arthchav/vitis/Fichiers/Weekly Report/~ Arthur Report/Séance n°06 - 06.12.22.pdf

Arthur | Rapport de séance n°6 | Projet Vitis
| | 6/12/22

Objectifs de la séance :

- Installation Arduino Mega
- Pouvoir brancher notre Robot à une prise 240v
- Installer le robot sur son nouveau châssis
- Coder les 2 capteurs IR pour faire tourner le robot

Réalisations :

- Le transfert de l’Arduino Uno à la Mega était nécessaire étant donné le nombre de pins nécessaire aux capteurs. Ce fût assez facile puisqu’il y a juste à recopier les branchements sur la nouvelle carte.

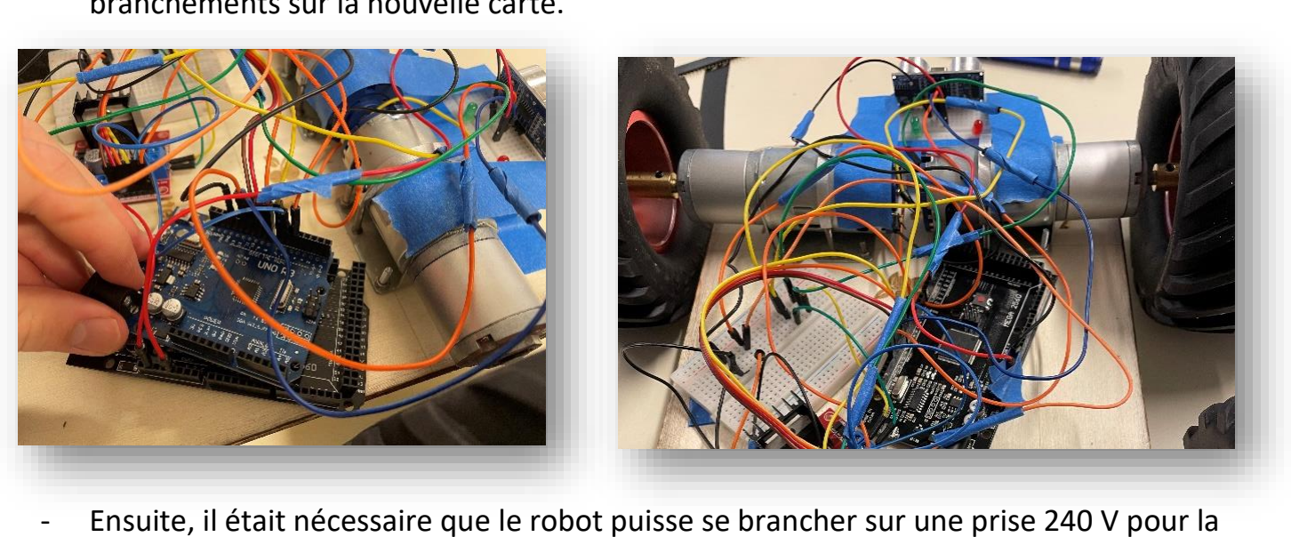
[picture p20: figure]

- Ensuite, il était nécessaire que le robot puisse se brancher sur une prise 240 V pour la suite de nos expériences. Jusqu’à présent nous utilisions les alimentations variables disponibles sur les paillasses.

Le professeur a pris de l’avance en faisant les branchements sur une alimentation afin de transformer le 240V alternatif en 12V continu.
Il fallait maintenant pouvoir alimenter la carte Arduino par le port prévu à cet effet ainsi que le Pont en H pour fournir l’énergie nécessaire aux moteurs.
Pour cela j’ai utilisé un domino d’électricien qui me permet d’obtenir 2 sorties. Enfin pour débrancher/brancher le tout facilement j’ai connecté une prise male femelle sur le domino et la sortie 12V. Montage ci-dessous.

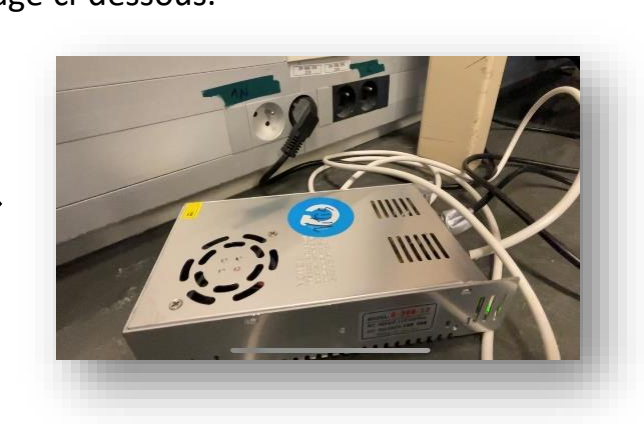
[picture p21: figure]
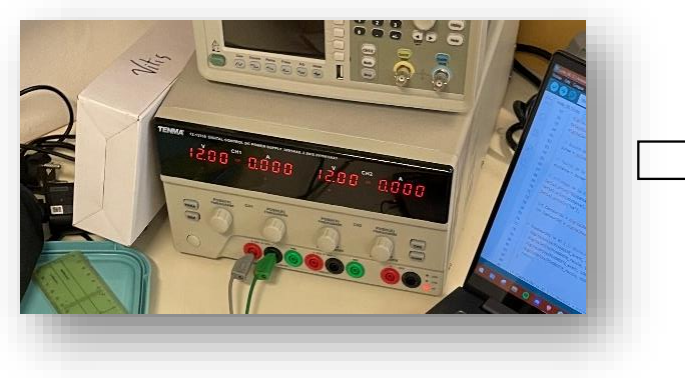
[picture p22: figure]

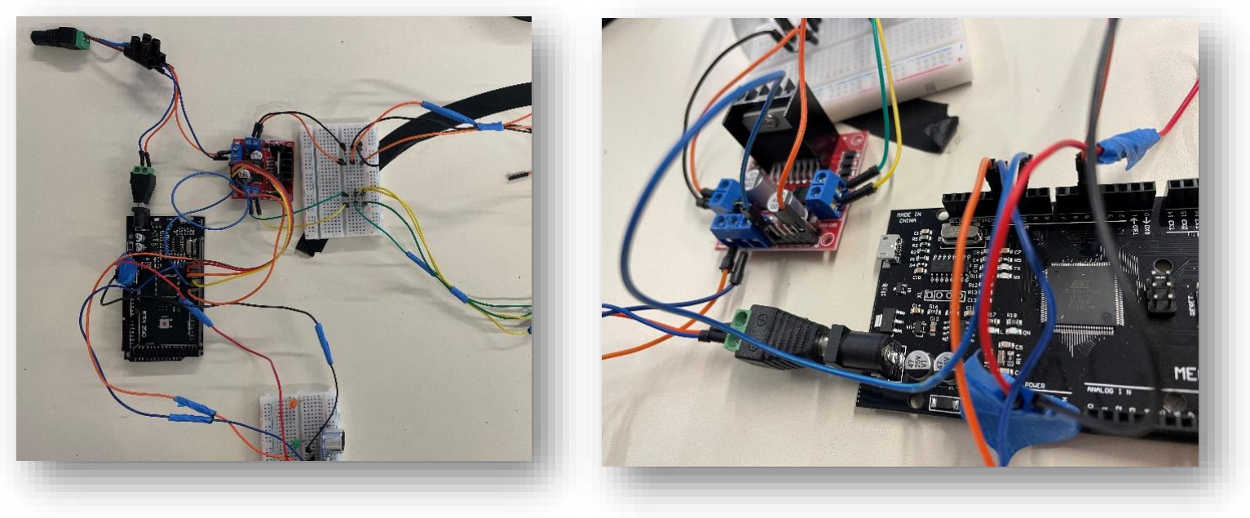
[picture p23: figure]

- Tanguy s’est chargé de fixer le robot sur le nouveau châssis et je me suis chargé de refaire les branchements un peu plus proprement.

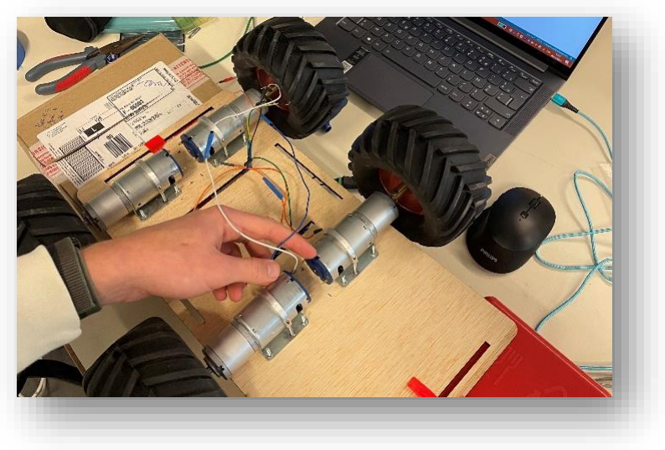
[picture p24: figure]

- Une fois cela il faut maintenant que notre robot puisse se diriger dans l’espace. Pour cela nous avons fait le choix de fixer 2 capteurs IR sur l’avant droite et gauche du robot.
Pour la partie code c’est assez simple (voir fin du doc).
- Un fois ce petit bout de code ajouté à l’ancien il était temps de faire fonctionner notre robot sur une prise 240V. Cependant plongé dans la réalisation du robot je n’ai pas réfléchi au fait que les câbles Arduino sont conçus pour transférer du 5V à basse intensité. Voici le résultat :

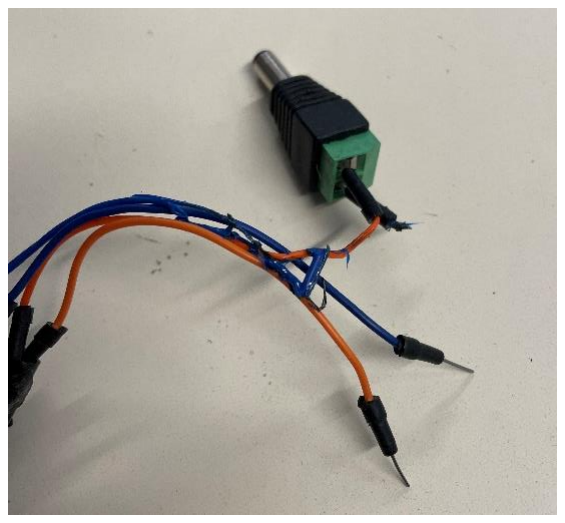
[picture p25: figure]

Des câbles complétement fondus. Reste plus qu’à changer ces câbles pour tester notre code !

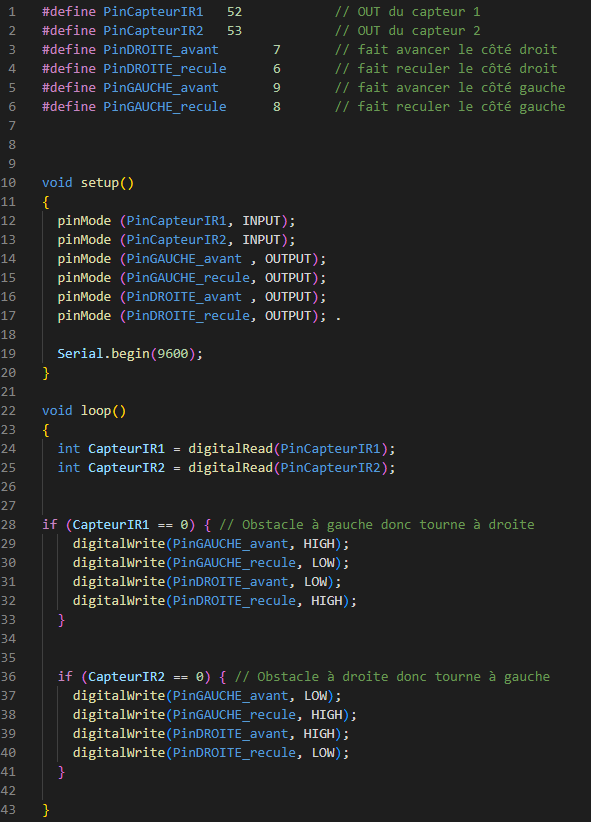
[picture p26: page 3]
