arthchav/vitis/Fichiers/Weekly Report/~ Tanguy Report/Rapport de séance n°9.pdf

Rapport de Séance 15/12/22

Objectifs de séance:
-Modélisation du porte-outils
I-Modélisation du porte-outils

Pendant cette séance j’ai continué la modélisation du porte-outils sur fusion, la difficulté est de réussir à avoir un ensemble cohérent et soudé afin d’avoir le résultat souhaité. J’ai rencontré beaucoup de difficulté afin que les pièces soient bien imbriqué et que les liaisons ce fasse bien.

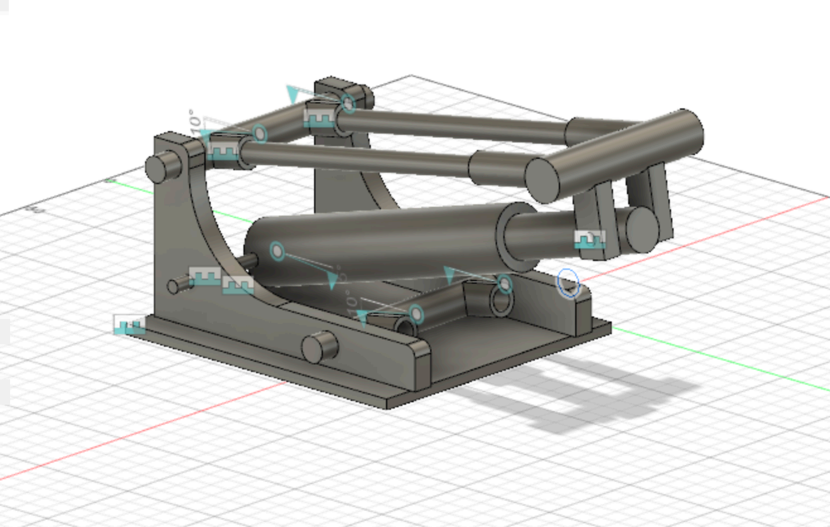
[picture p83: figure]

L’objectif pour la rentré est d’obtenir une modélisation satisfaisante afin de lancer l’impression des pièces.
