arthchav/vitis/Fichiers/Weekly Report/~ Arthur Report/Séance n°03 - 28.10.22.pdf

Arthur | Rapport de séance n°3 | Projet Vitis
| | 28/10/22

Objectifs de la séance :

- Découper le châssis
- Découverte GPS et tenter d’avoir une position

Réalisations :

- J’ai consacré la première partie de la séance à la découpe du châssis, le fichier svg étant prêt depuis la semaine dernière il ne restait plus qu’à lancer l’impression. Afin de pourvoir fixer le moteur et la batterie, le châssis (en bois) se devait d’être le plus rigide possible.
Le contreplaqué 5 mm était donc une bonne solution.

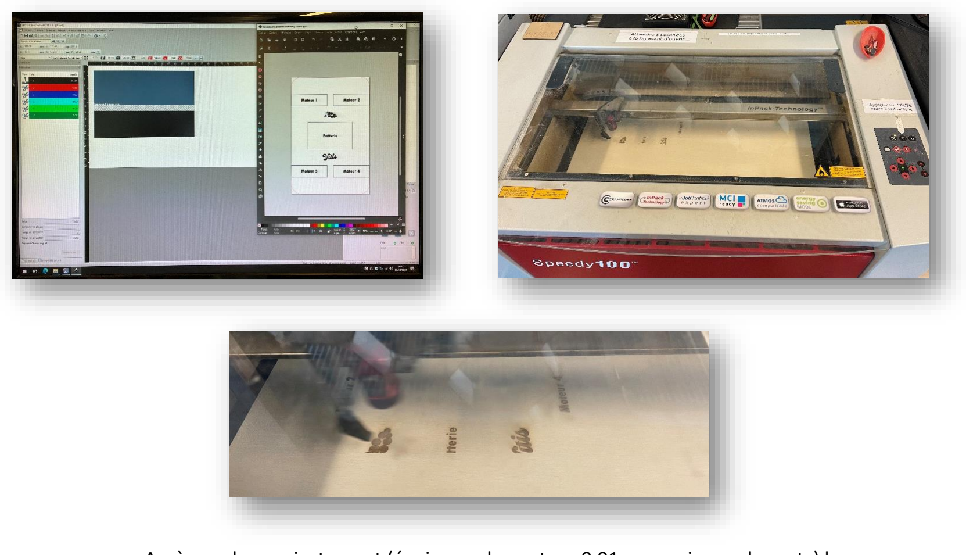
[picture p94: figure]

Après quelques ajustement (épaisseur du contour 0.01, mauvaise couleur etc) la gravure s’est bien déroulée.
Le problème est que le FabLab ont de nouveaux fournisseurs de bois, le contreplaqué 5 mm fournit ne se découpait pas avec les paramètres 5 mm de la machine. Après plusieurs essais de découpe sur une chute de ce même bois, la solution était de faire 5 fois la même découpe en diminuant la vitesse de la tête.

Le problème est que diminuer la vitesse de la tête ou augmenter la puissance du laser provoque l’appartion d’une flamme, celle-ci brûle et tâche le bois en plus d’être un danger si elle n’est pas contrôlée.

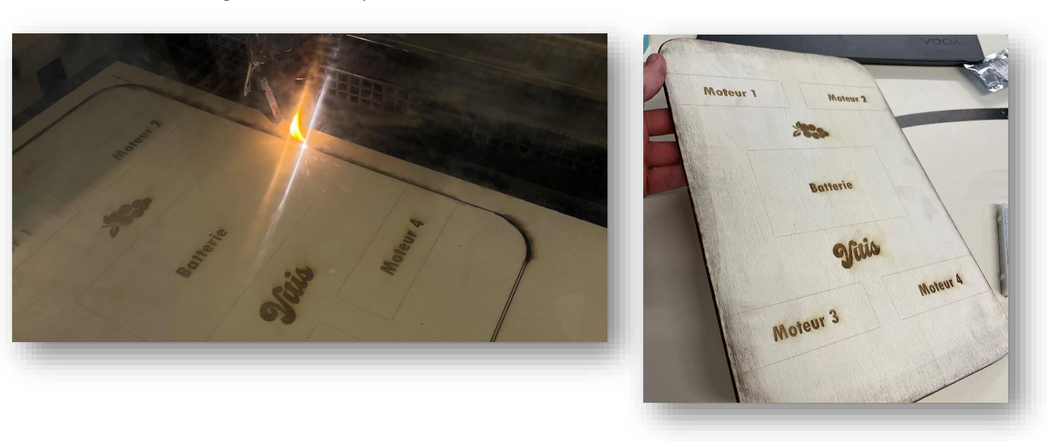
[picture p95: figure]

- Une fois le châssis terminé, découverte du GPS NEO-6M récupérer la semaine dernière. L’antenne et la carte électronique ont été accroché ensemble pour empêcher la rupture du fil (fragile) qui les relies.

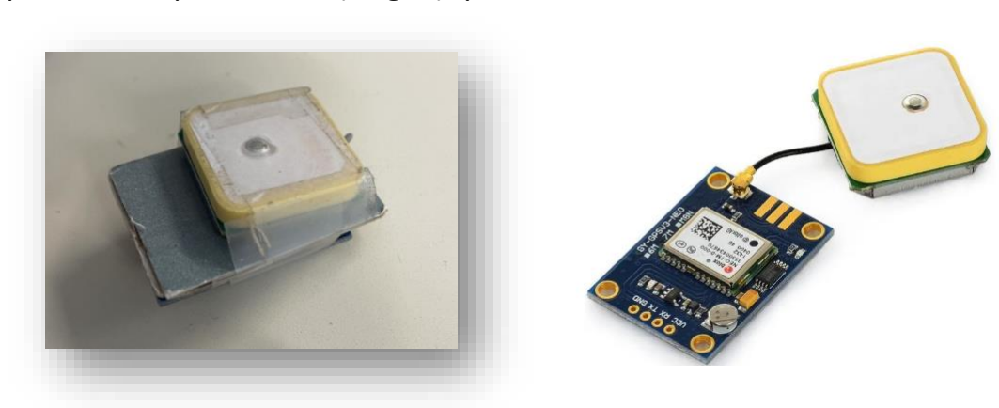
[picture p96: figure]

Le premier objectif est d’obtenir les données sans traitement pour la lisibilité en sortie de capteur. Les données se présentent sous cette forme :

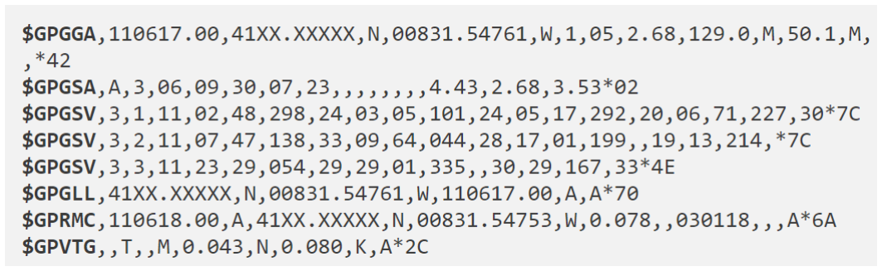
[picture p97: figure]

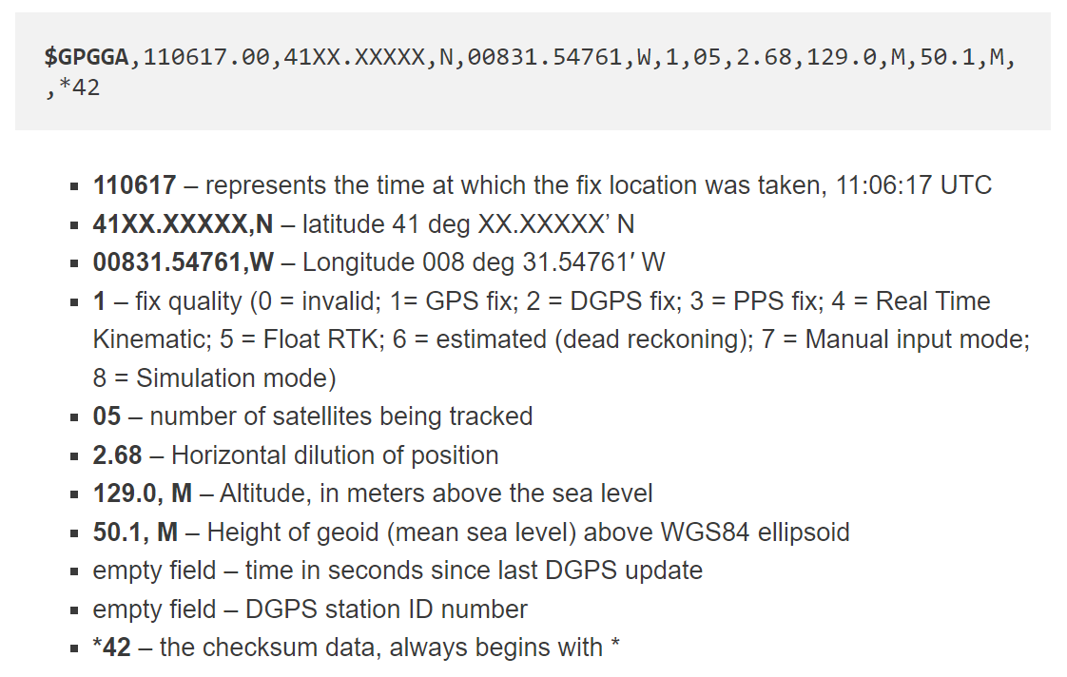
[picture p98: figure]

$GPGGA est le paramètre qui nous intéresse avec la longitude/latitude et donc la position de notre robot. Or en réalité voici ce que j’ai obtenu :

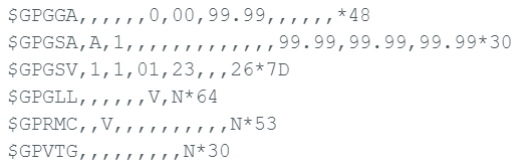
[picture p99: figure]

Le problème peut venir d’un problème de bibliothèque ou du capteur en lui-même. Pour la prochaine séance je n’utiliserai pas ce capteur pour voir si le problème vient de là.
