arthchav/vitis/Fichiers/~ Polytech/NVIDIA/TD-9-11-22/Arthur/setup-mysql.pdf

### Réalisation d’un script de sauvegarde de base de données

I- Installer MySQL

- Sous Xubuntu pour installer une application on utilise la commande « apt install ». On utilise
| « sudo » pour les droits utilisateurs puis on installe en veillant à ce que apt soit à jour avec « apt update » :
II- | Importer la base de données
- Tout d’abord il faut la télécharger. Pour ma part j’ai utiliser le navigateur Firefox intégré à
| Xubuntu pour télécharger le fichier suivant : https://www.mysqltutorial.org/wp- content/uploads/2018/03/mysqlsampledatabase.zip (https://www.mysqltutorial.org/wp-content/uploads/2018/03/mysqlsampledatabase.zip)
| Une fois télécharger il faut le « Unzip », si comme moi vous obtenez le fichier « mysqlsampledatabase.sql » sur le bureau, vous pouvez le déplacer à la racine avec la commande : « mv « mysqlsampledatabase.sql /~ »
- Une fois le fichier obtenu, on va créer notre base de données à partir de ce ficher backup (on prend l’utilisateur « root » pour les droits). Puis on peut enfin entrer dans mysql :

sudo apt update

sudo apt install mysql-server

sudo mysql -u root < /home/arthur/mysqlsampledatabase.sql

sudo mysql -u root

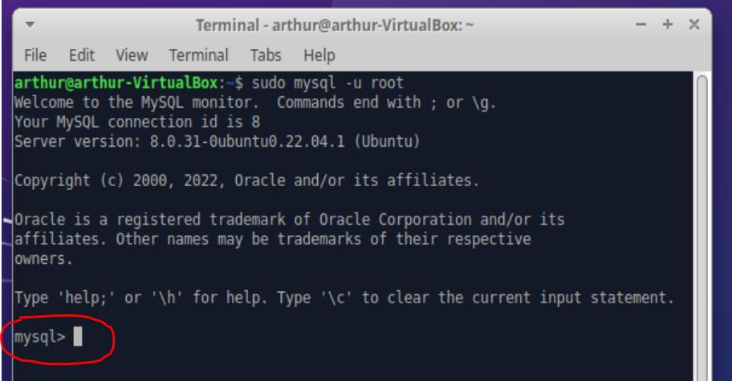
[picture p108: figure]

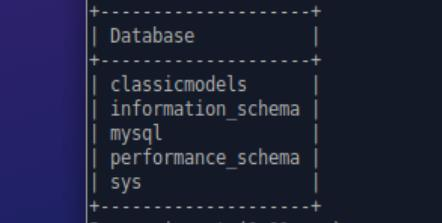
[picture p109: figure]

- On peut vérifier en listant nos bases de données :

mysql>show databases;
