arthchav/vitis/Fichiers/MPU_6050 on Vitis/VITIS MPU 6050 Presentation.pdf

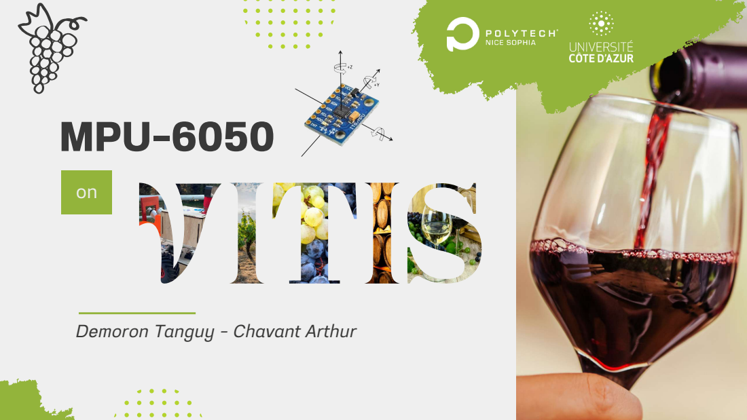
[picture p110: page 1]
MPU-6050

Demoron Tanguy - Chavant Arthur

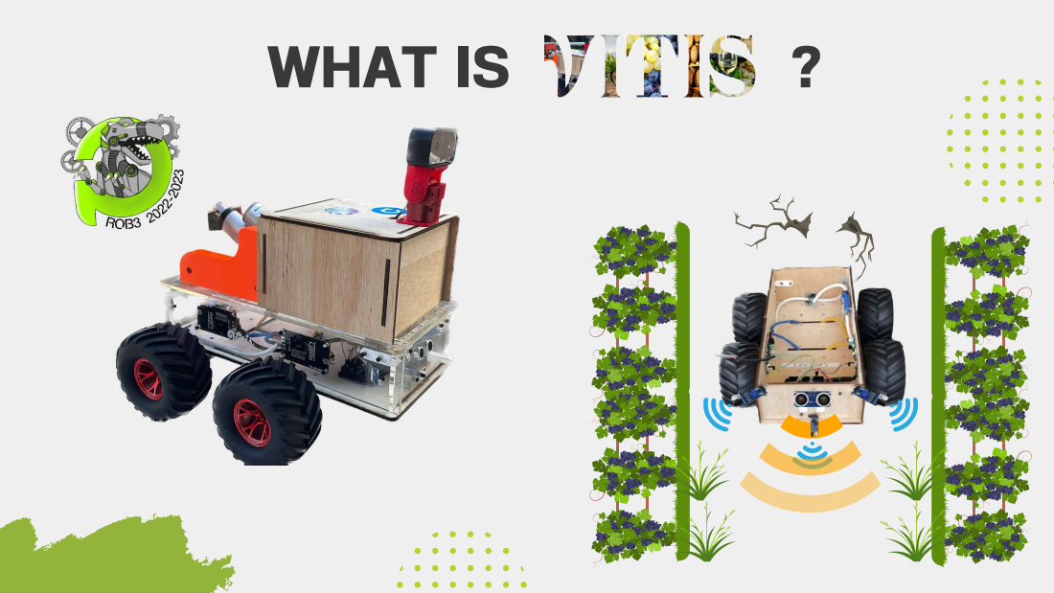
[picture p111: page 2]
WHAT IS

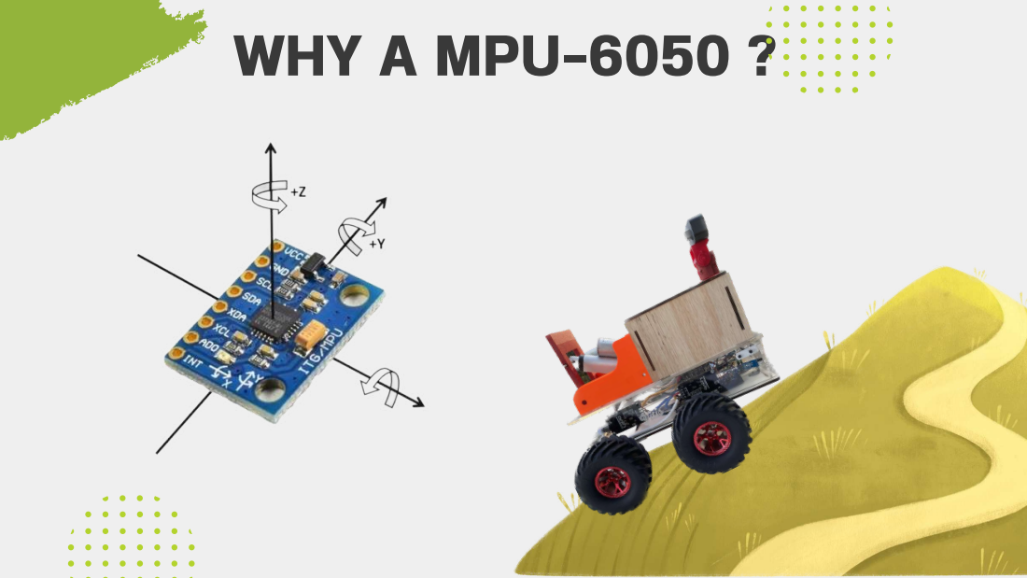
[picture p112: page 3]
WHY A MPU-6050 ?

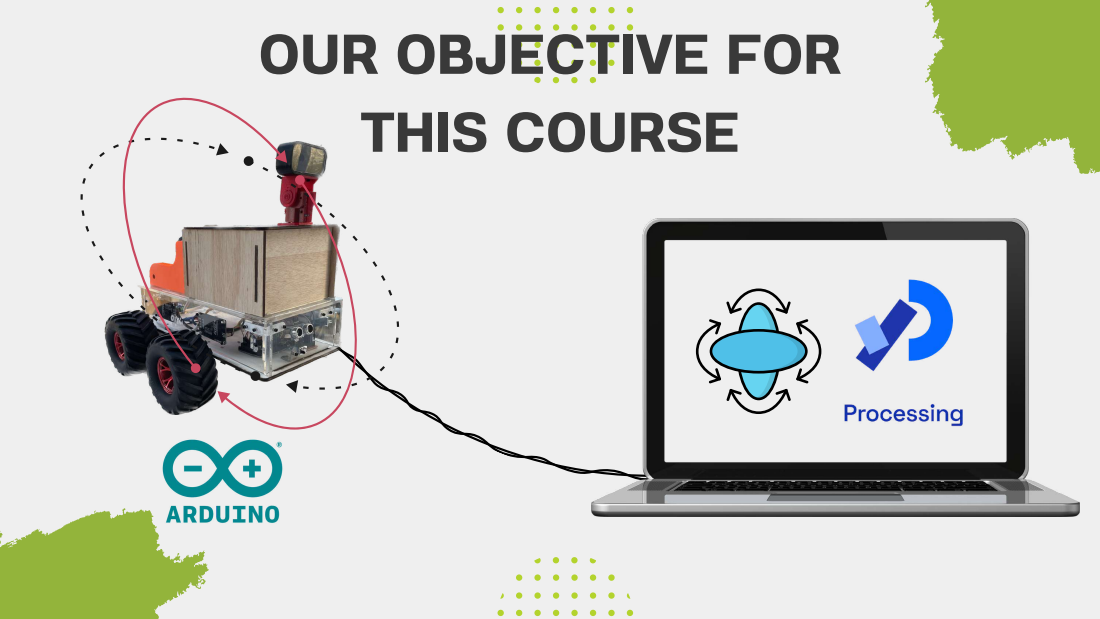
[picture p113: page 4]

OUR OBJECTIVE FOR
THIS COURSE

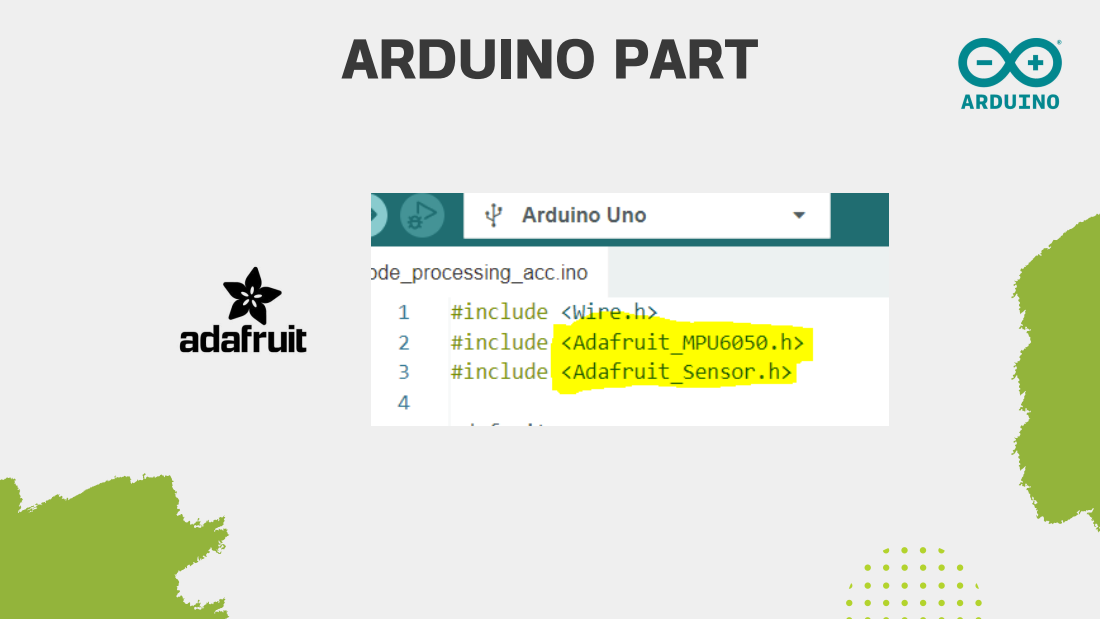
[picture p114: page 5]
ARDUINO PART

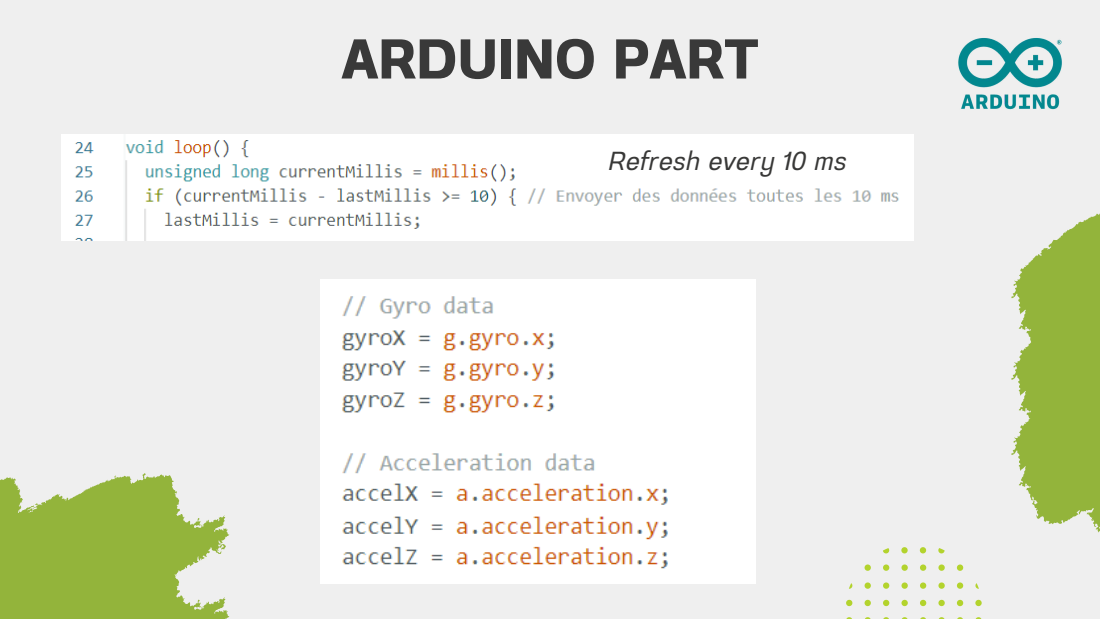
[picture p115: page 6]
ARDUINO PART

Refresh every 10 ms

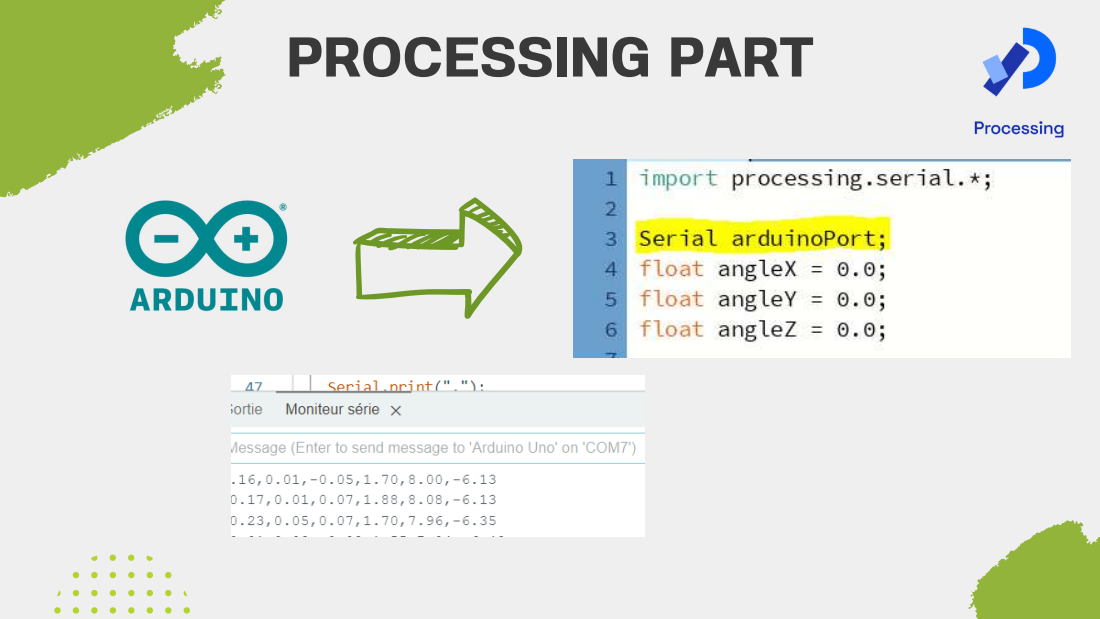
[picture p116: page 7]
PROCESSING PART

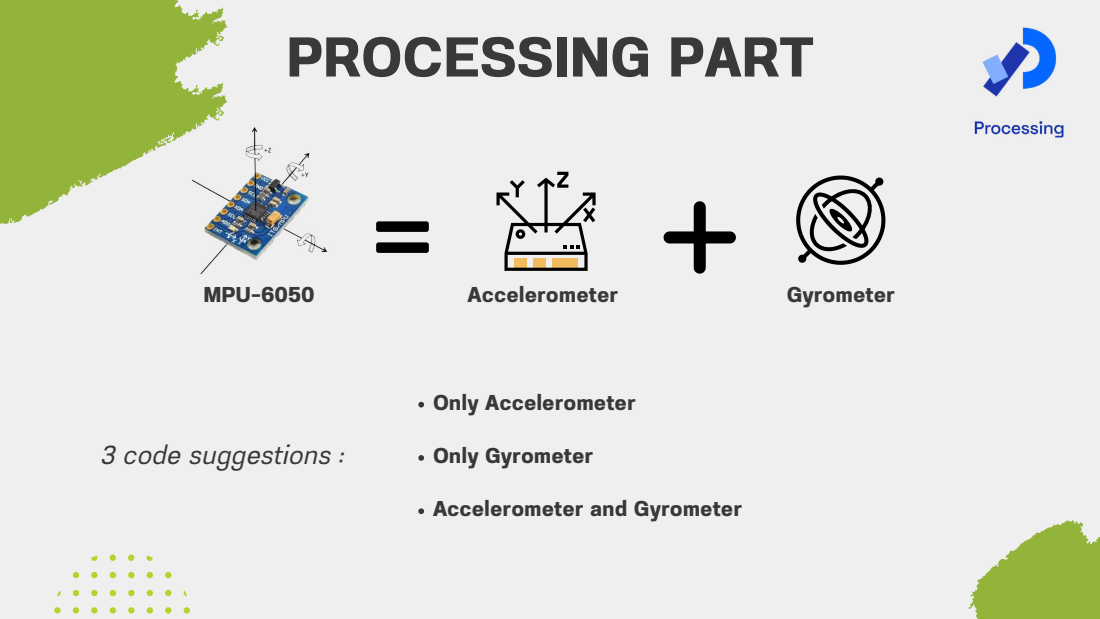
[picture p117: page 8]
PROCESSING PART; 3 code suggestions :; MPU-6050; Accelerometer; Gyrometer; Only Accelerometer; Only Gyrometer

Accelerometer and Gyrometer

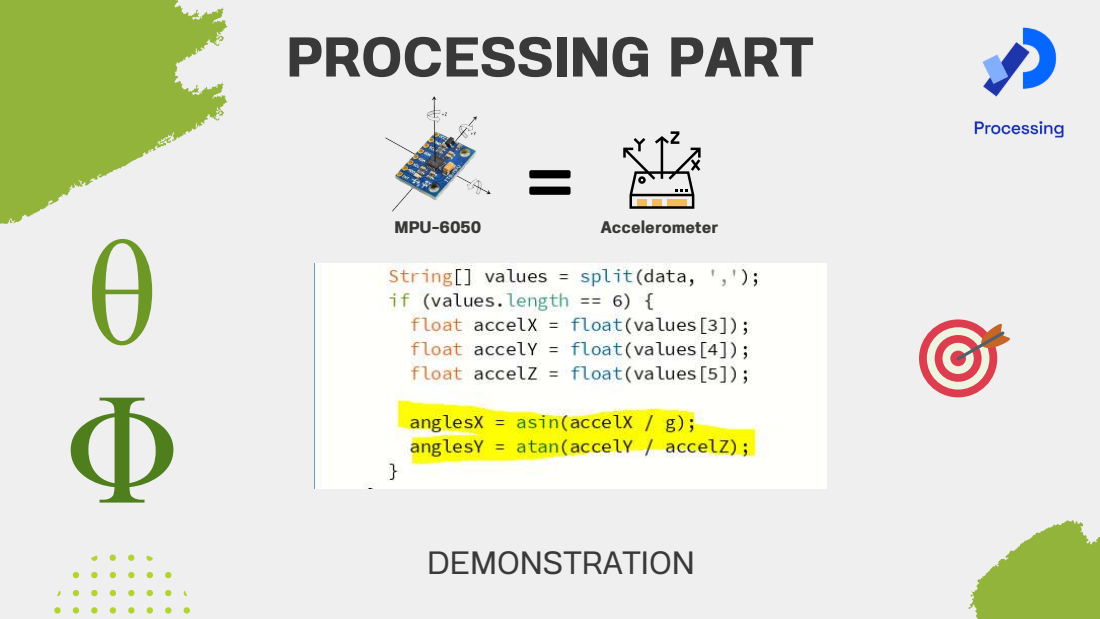
[picture p118: page 9]
PROCESSING PART; MPU-6050; Accelerometer; DEMONSTRATION

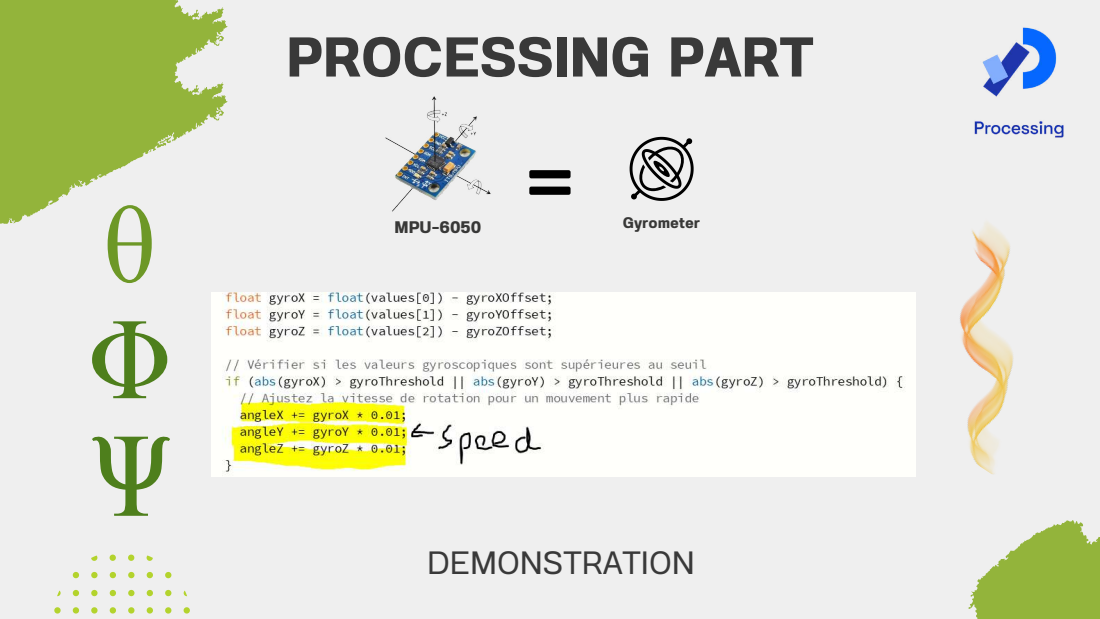
[picture p119: page 10]
PROCESSING PART; MPU-6050; Gyrometer; DEMONSTRATION

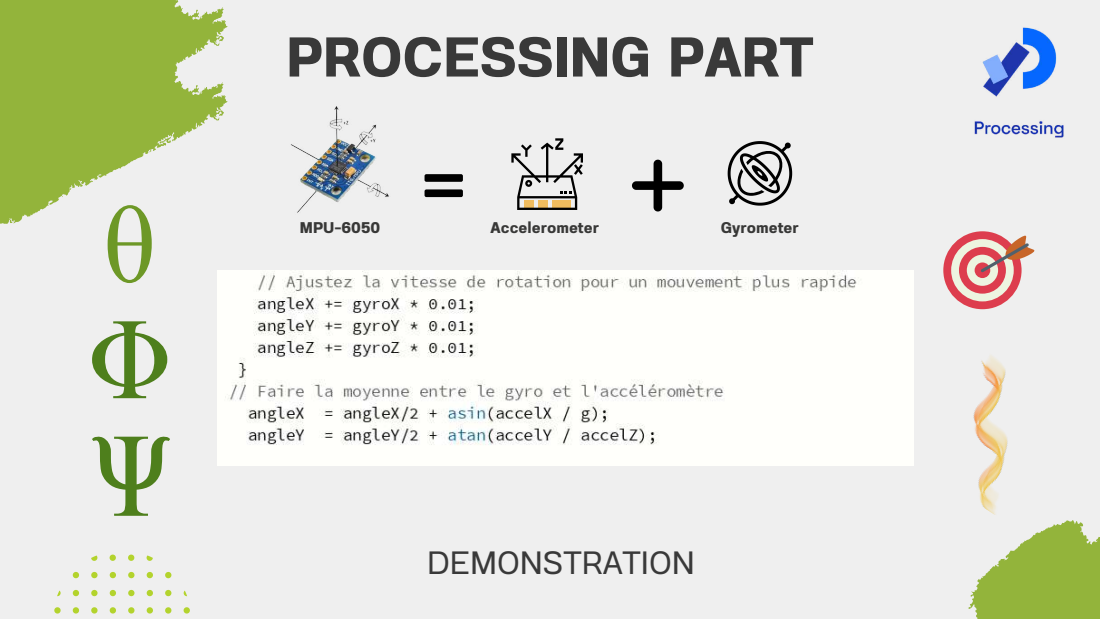
[picture p120: page 11]
PROCESSING PART; MPU-6050; Accelerometer; Gyrometer; DEMONSTRATION

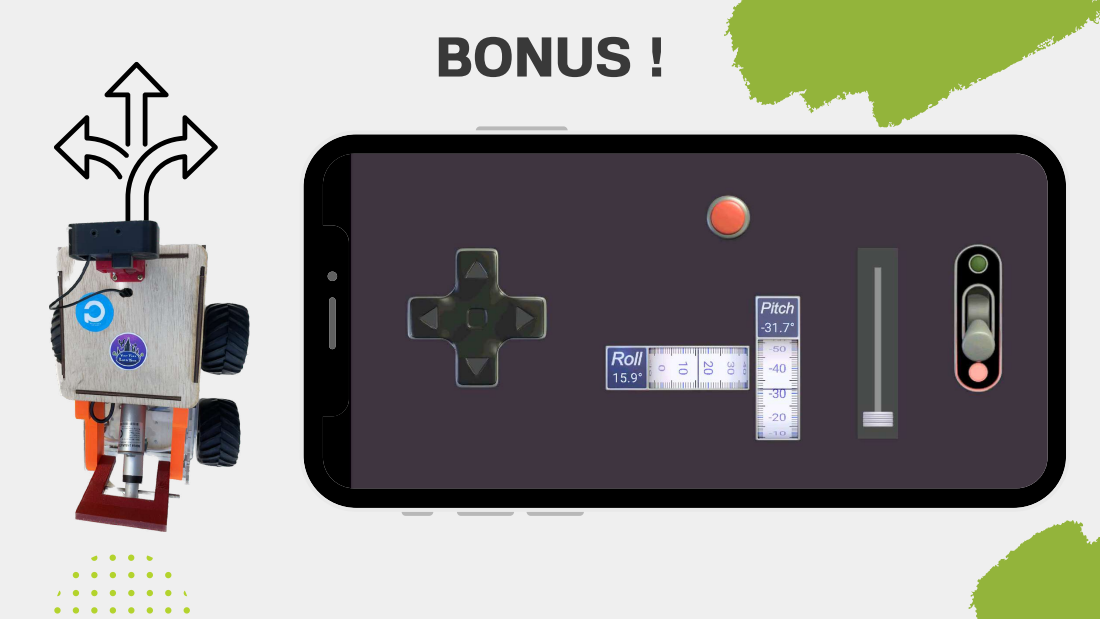
[picture p121: page 12]
BONUS !

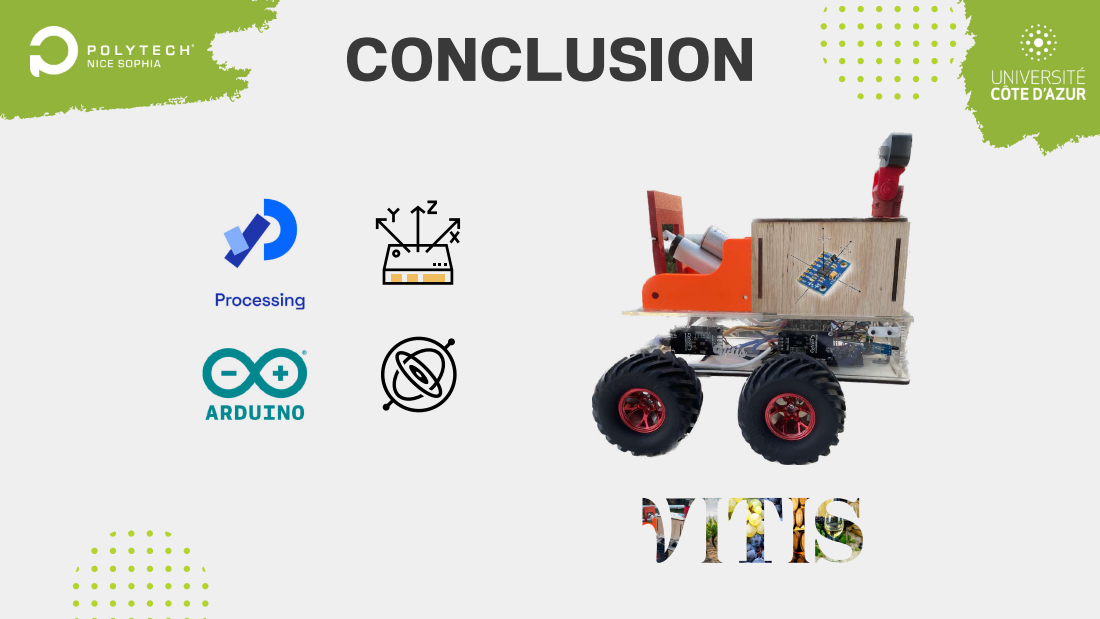
[picture p122: page 13]
CONCLUSION
