arthchav/vitis/Fichiers/~ Polytech/Tanguy Work/Code Morse (Avec timer)/CodeMorse.ino

#include "Traducteur.hpp"
#include "LettreMorse.hpp"

LettreMorse Lm;
Traducteur Tr;

void setup() { 

  Serial.begin(9600);
  pinMode(LED_BUILTIN, OUTPUT);
}

void loop() {

if (Serial.available()){
      Lm.mot = Serial.readString();
      Lm.ConversionMorse();
      Tr.traducteurmillis(Lm.morse);
}

}
